strlentv/teletext-is-not-dead/src/drv_stm32/drv_video.h

/*! *******************************************************************************************************
* Copyright (c) 2018-2019 K. Sz. Horvath
*
* All rights reserved
*
* \file drv_video.h
*
* \brief Low-level video driver for STM32
*
* \author K. Sz. Horvath
*
**********************************************************************************************************/

#ifndef DRV_VIDEO_H
#define DRV_VIDEO_H

//--------------------------------------------------------------------------------------------------------/
// Include files
//--------------------------------------------------------------------------------------------------------/


//--------------------------------------------------------------------------------------------------------/
// Definitions
//--------------------------------------------------------------------------------------------------------/


//--------------------------------------------------------------------------------------------------------/
// Types
//--------------------------------------------------------------------------------------------------------/


//--------------------------------------------------------------------------------------------------------/
// Global variables
//--------------------------------------------------------------------------------------------------------/


//--------------------------------------------------------------------------------------------------------/
// Interface functions
//--------------------------------------------------------------------------------------------------------/
void DrvVideo_Init( void );
void DrvVideo_HorizontalSyncIT( void );
void DrvVideo_TeletextSendCompletedIT( void );


#endif  // DRV_VIDEO_H

//-----------------------------------------------< EOF >--------------------------------------------------/
